etank7000/Micromouse/user/inc/gyro.h

#ifndef GYRO_H
#define GYRO_H

#include "main.h"
#include "stm32f4xx_hal.h"

// MPU6000 registers
#define MPUREG_XG_OFFS_TC 0x00
#define MPUREG_YG_OFFS_TC 0x01
#define MPUREG_ZG_OFFS_TC 0x02
#define MPUREG_X_FINE_GAIN 0x03
#define MPUREG_Y_FINE_GAIN 0x04
#define MPUREG_Z_FINE_GAIN 0x05
#define MPUREG_XA_OFFS_H 0x06
#define MPUREG_XA_OFFS_L 0x07
#define MPUREG_YA_OFFS_H 0x08
#define MPUREG_YA_OFFS_L 0x09
#define MPUREG_ZA_OFFS_H 0x0A
#define MPUREG_ZA_OFFS_L 0x0B
#define MPUREG_PRODUCT_ID 0x0C
#define MPUREG_SELF_TEST_X 0x0D
#define MPUREG_SELF_TEST_Y 0x0E
#define MPUREG_SELF_TEST_Z 0x0F
#define MPUREG_SELF_TEST_A 0x10
#define MPUREG_XG_OFFS_USRH 0x13
#define MPUREG_XG_OFFS_USRL 0x14
#define MPUREG_YG_OFFS_USRH 0x15
#define MPUREG_YG_OFFS_USRL 0x16
#define MPUREG_ZG_OFFS_USRH 0x17
#define MPUREG_ZG_OFFS_USRL 0x18
#define MPUREG_SMPLRT_DIV 0x19
#define MPUREG_CONFIG 0x1A
#define MPUREG_GYRO_CONFIG 0x1B
#define MPUREG_ACCEL_CONFIG 0x1C
#define MPUREG_INT_PIN_CFG 0x37
#define MPUREG_INT_ENABLE 0x38
#define MPUREG_ACCEL_XOUT_H 0x3B
#define MPUREG_ACCEL_XOUT_L 0x3C
#define MPUREG_ACCEL_YOUT_H 0x3D
#define MPUREG_ACCEL_YOUT_L 0x3E
#define MPUREG_ACCEL_ZOUT_H 0x3F
#define MPUREG_ACCEL_ZOUT_L 0x40
#define MPUREG_TEMP_OUT_H 0x41
#define MPUREG_TEMP_OUT_L 0x42
#define MPUREG_GYRO_XOUT_H 0x43
#define MPUREG_GYRO_XOUT_L 0x44
#define MPUREG_GYRO_YOUT_H 0x45
#define MPUREG_GYRO_YOUT_L 0x46
#define MPUREG_GYRO_ZOUT_H 0x47
#define MPUREG_GYRO_ZOUT_L 0x48
#define MPUREG_SIGNAL_PATH_RESET 0x68
#define MPUREG_USER_CTRL 0x6A
#define MPUREG_PWR_MGMT_1 0x6B
#define MPUREG_PWR_MGMT_2 0x6C
#define MPUREG_BANK_SEL 0x6D
#define MPUREG_MEM_START_ADDR 0x6E
#define MPUREG_MEM_R_W 0x6F
#define MPUREG_DMP_CFG_1 0x70
#define MPUREG_DMP_CFG_2 0x71
#define MPUREG_FIFO_COUNTH 0x72
#define MPUREG_FIFO_COUNTL 0x73
#define MPUREG_FIFO_R_W 0x74
#define MPUREG_WHOAMI 0x75
#define MPUREG_INTERRUPT_STATUS 0x3A

// Configuration bits MPU6000
#define BIT_SLEEP 0x40
#define BIT_H_RESET 0x80
#define BITS_CLKSEL 0x07
#define MPU_CLK_SEL_PLLGYROX 0x01
#define MPU_CLK_SEL_PLLGYROZ 0x03
#define MPU_EXT_SYNC_GYROX 0x02
#define BITS_FS_250DPS 0x00
#define BITS_FS_500DPS 0x08
#define BITS_FS_1000DPS 0x10
#define BITS_FS_2000DPS 0x18
#define BITS_FS_2G 0x00
#define BITS_FS_4G 0x08
#define BITS_FS_8G 0x10
#define BITS_FS_16G 0x18
#define BITS_FS_MASK 0x18
#define BITS_DLPF_CFG_256HZ_NOLPF2 0x00
#define BITS_DLPF_CFG_188HZ 0x01
#define BITS_DLPF_CFG_98HZ 0x02
#define BITS_DLPF_CFG_42HZ 0x03
#define BITS_DLPF_CFG_20HZ 0x04
#define BITS_DLPF_CFG_10HZ 0x05
#define BITS_DLPF_CFG_5HZ 0x06
#define BITS_DLPF_CFG_2100HZ_NOLPF 0x07
#define BITS_DLPF_CFG_MASK 0x07
#define BIT_INT_ANYRD_2CLEAR 0x10
#define BIT_RAW_RDY_EN 0x01
#define BIT_I2C_IF_DIS 0x10

#define READ_FLAG 0x80

/**
 * @brief Initializes the gyroscope for SPI.
 */
void gyroSPIInit(void);

/**
 * @brief Set the right range for the gyroscopes.
 */
void setGyroScale(void);

/**
 * @brief Read the gyroscope z-axis rotation.
 * @retval 16-bit value of z-axis gyroscope register.
 */
int16_t readGyro(void);

/**
 * @brief Read the who_am_i register of the gyro and print to the terminal
 */
void gyroWHOAMI(void);

/**
 * @brief Calibrate the gyro adn set the reference value
 */
void calibrateGyro(void);

/**
 * @brief Update the gyro angle every systick
 */
void updateGyroAngle(void);

/**
 * @brief Reset the gyro angle to 0 (to get rid of drift, used right before a turn)
 */
void resetGyroAngle(void);

/**
 * @breif Read the gyro angle 
 * @retval float value of the angle of the gyroscope
 */
float getGyroAngle(void);

/**
 * @breif Read the gyro out z 
 * @retval 16-bit value of the outz of the gyroscope
 */
int16_t getGyroOutZ(void);

#endif // GYRO_H
