etank7000/Micromouse/user/inc/stack.h

/**
 * @file    stack.h
 * @brief   Fixed size global Cell stack.
 *
 * The stack can hold a maximum of 512 elements.
 */

/**
 * @brief A location in the maze, represented by (x, y).
 *
 * The mouse always starts in Cell (0, 0).
 */

#ifndef MAZE_STACK_H
#define MAZE_STACK_H

typedef struct Cell
{
  unsigned short x;    /**< x-coordinate */
  unsigned short y;    /**< y-coordinate */
} Cell;

/**
 * @brief Push a value onto the stack
 *
 * @param v The value to push
 * @retval 0 if successful, -1 if stack is full
 */
int stack_push(unsigned short x, unsigned short y);

/**
 * @brief Remove the element on top of the stack.
 *
 * @retval 0 if successful, -1 if stack is empty
 */
int stack_pop(void);

/**
 * @brief Access the top element in the stack.
 * @return The top element in the stack
 */
Cell stack_top(void);

/**
 * @brief Check whether the stack is empty.
 *
 * @retval 1 if the stack is empty, 0 otherwise
 */
int stack_empty(void);

#endif  // MAZE_STACK_H
